harryxni/TopmetalSe-V1/Hardware/Images/chip_microscope_pictures/large.jpg

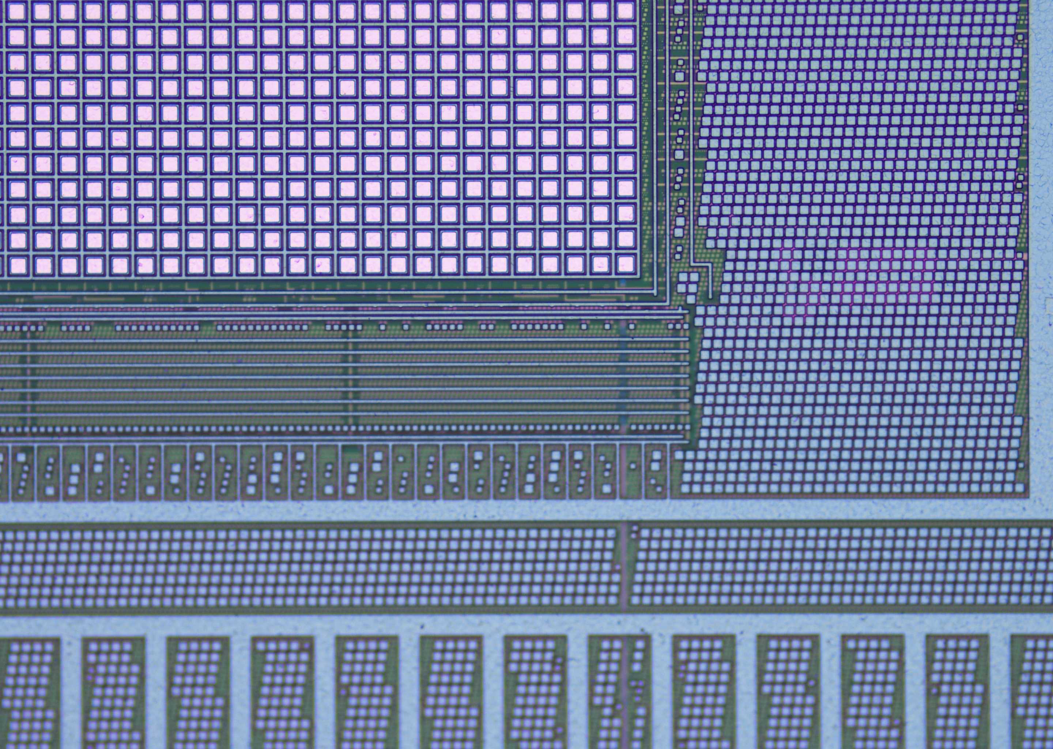
Hardware/Images/chip_microscope_pictures/large.jpg
