harryxni/TopmetalSe-V1/Hardware/TopmetalSe/caravel_floorplan.jpg

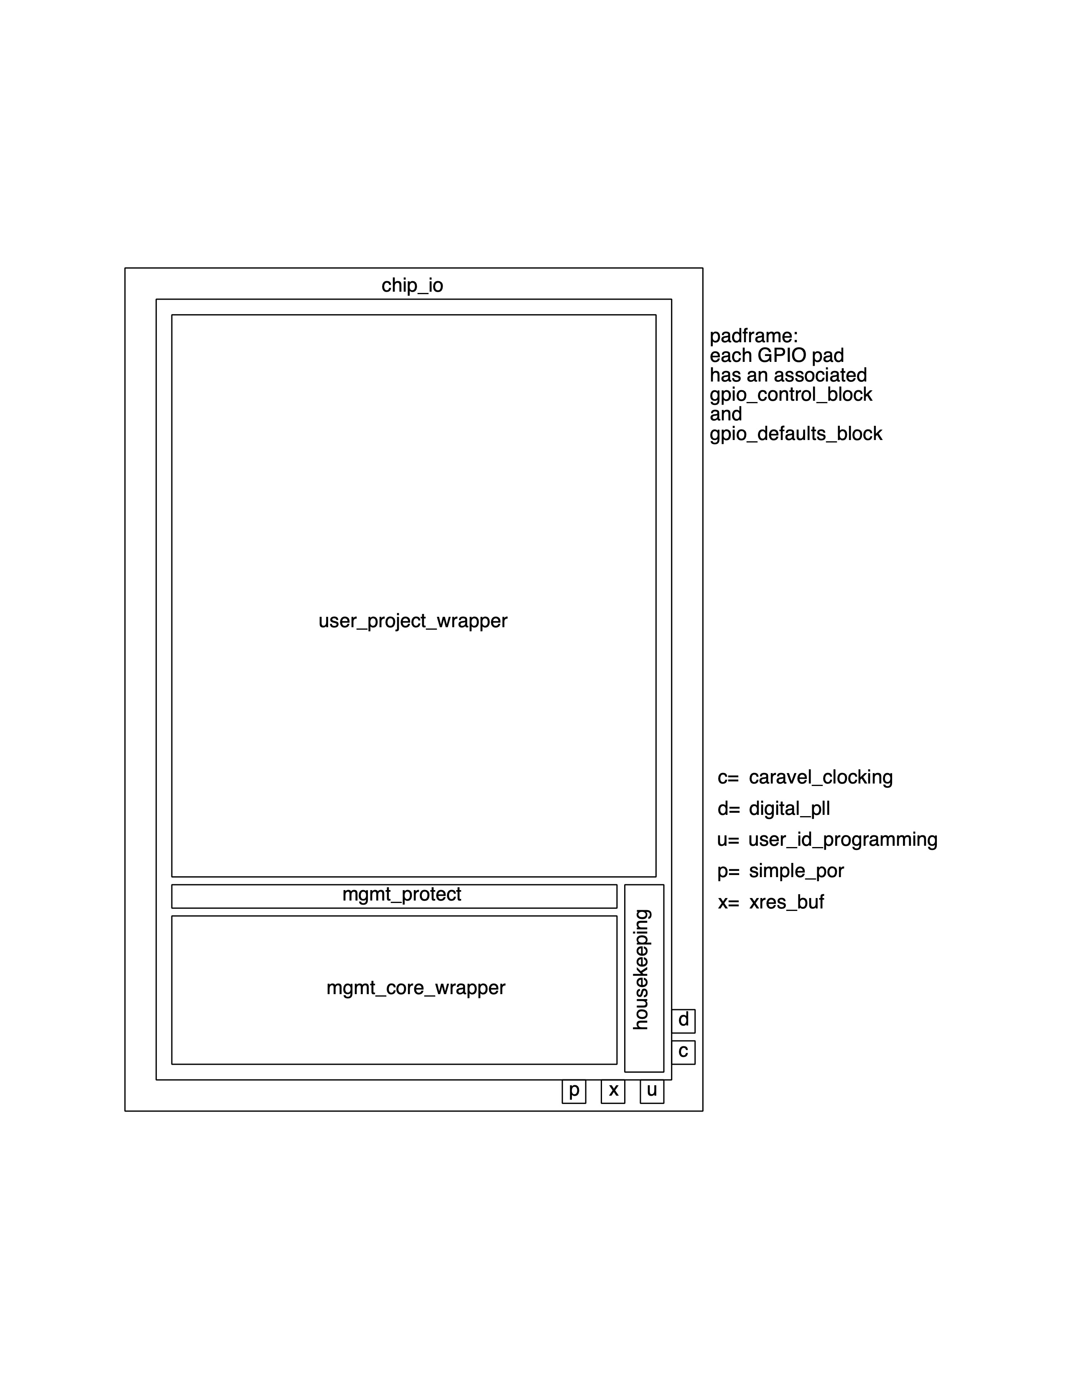
Hardware/TopmetalSe/caravel_floorplan.jpg
