harryxni/TopmetalSe-V1/Hardware/TopmetalSe/pad_structure.png

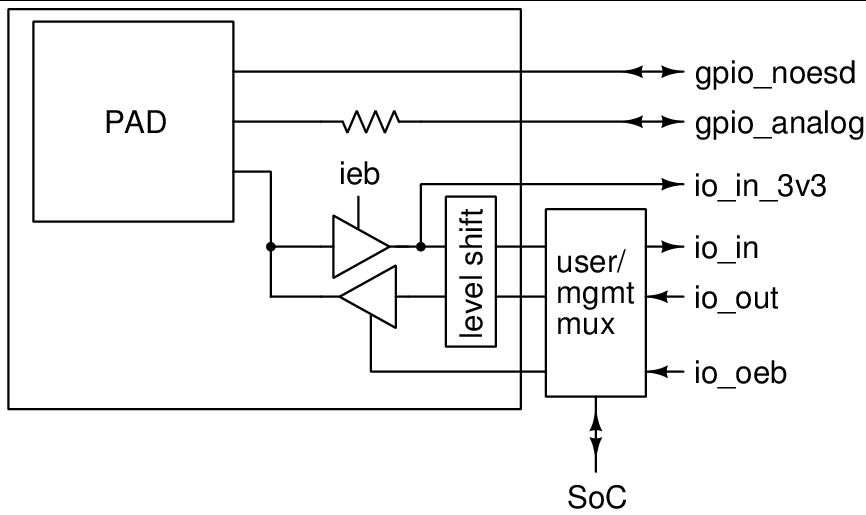
Hardware/TopmetalSe/pad_structure.png
