harryxni/TopmetalSe-V1/Hardware/Test_Board/annotated_PCB.png

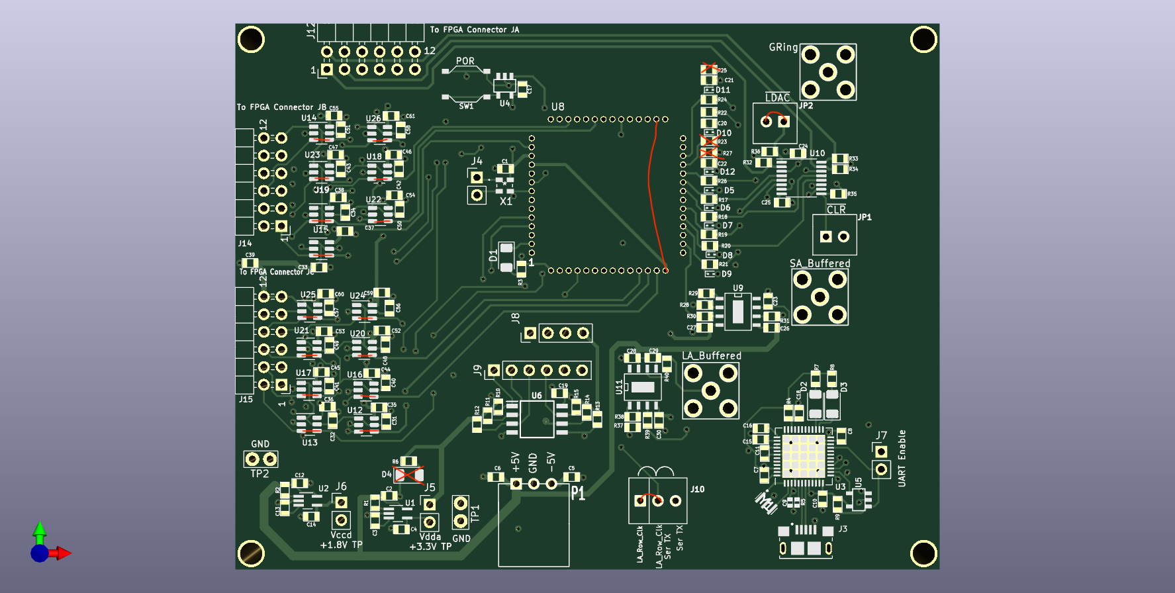
Hardware/Test_Board/annotated_PCB.png
