harryxni/TopmetalSe-V1/Results/Photoelectric/led_trigger_gifs/frames_60V.gif

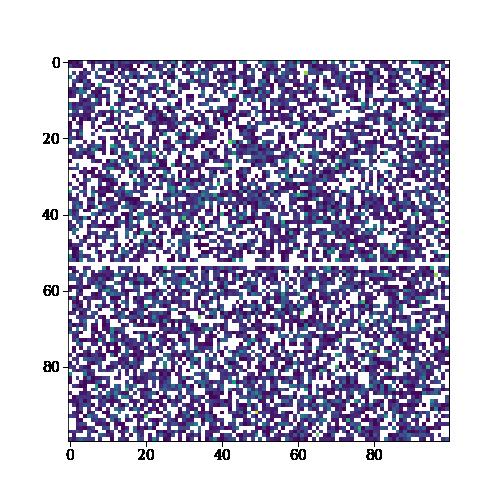
Results/Photoelectric/led_trigger_gifs/frames_60V.gif
