harryxni/TopmetalSe-V1/Results/Photoelectric/led_trigger_gifs/frames_120V.gif

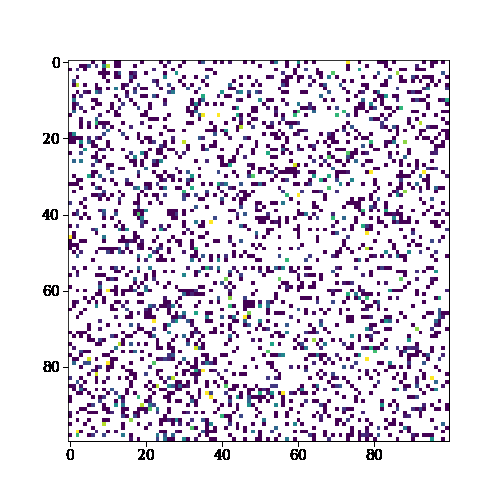
Results/Photoelectric/led_trigger_gifs/frames_120V.gif
